MOSH-Insa-Toulouse/4GP-23_24-Briens_Charnay/Circuit_capteur_final.asc

C1: cap; 100n
C2: cap; 100n
C4: cap; 1µ
R1: res; 100k
R2: res; 1k
R3: res; 100k
R5: res; 10k
R6: res; 1k
U1: LTC1050
V1: voltage; 5
V2: voltage; 5
X1: capteur_graphite
Named nets: 0, ADC
.tran 2
;ac dec 100 0.1 0.1G
.param G0 10n
.param G1 10n
.param R1 100k
